cribnez/telemonitoring-geriatric-vitals-iot/images/img5.jpg

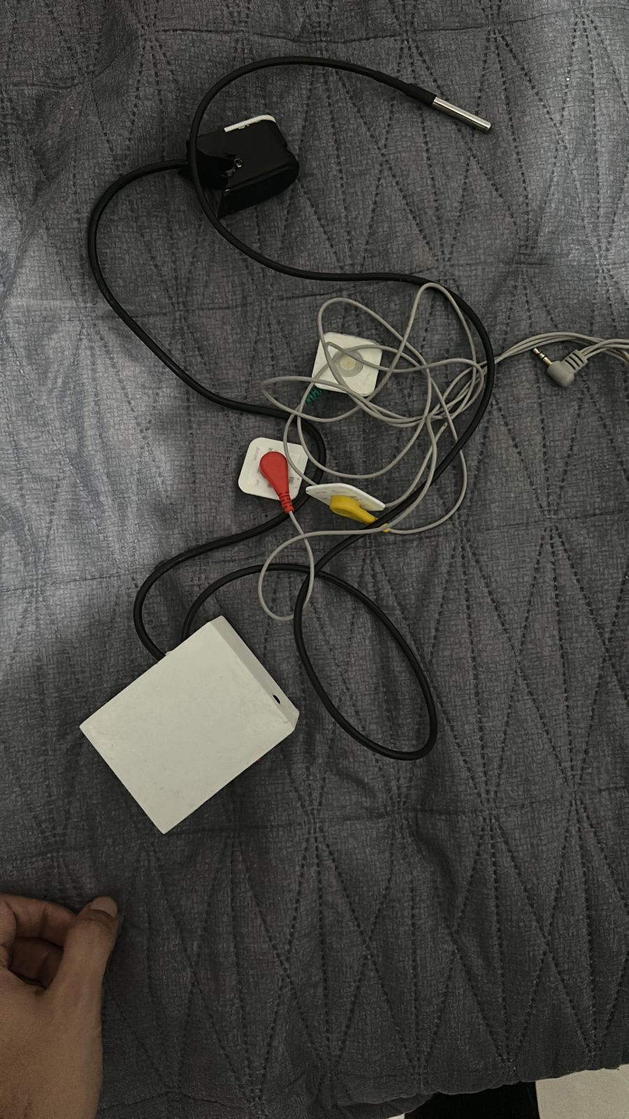
images/img5.jpg
